pjaos/drive_mobility_scooter_battery_dock/schematic/drive_mobility_scooter_battery_dock.kicad_sch

## KiCad design schematic/drive_mobility_scooter_battery_dock.kicad_sch (2025-09-18, an earlier design)

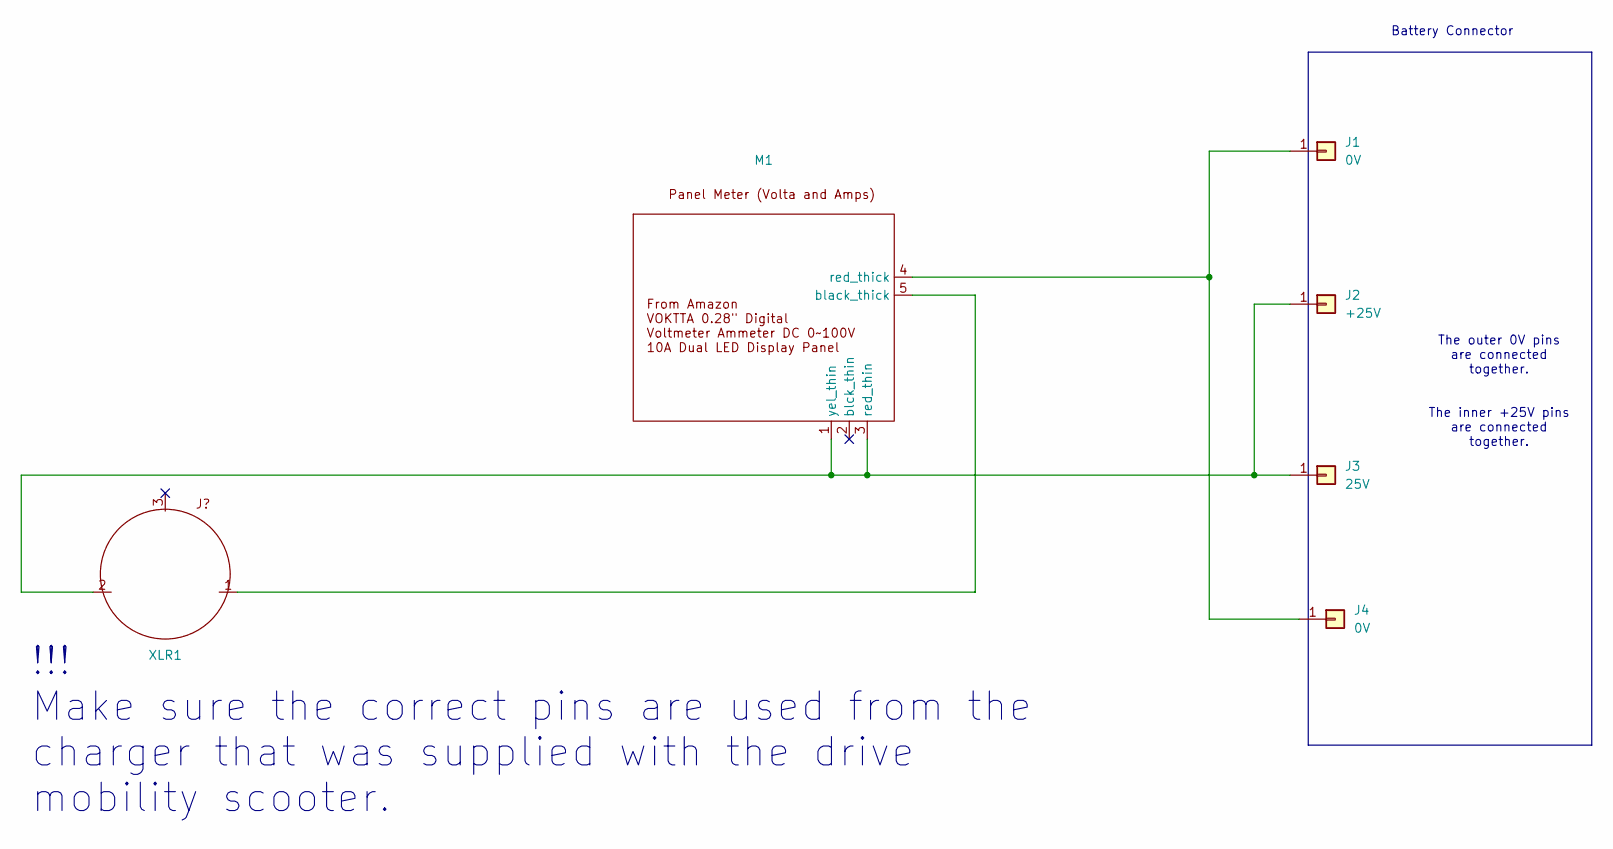
[picture p12: schematic drive_mobility_scooter_battery_dock.kicad_sch]

Parts:
J1, J4: 0V
J2: +25V
J3: 25V
M1: (no value)
XLR1: (no value)

Connections:
unnamed: J1.1, J4.1, M1.4 (red_thick)
unnamed: J2.1, J3.1, M1.1 (yel_thin), M1.3 (red_thin), XLR1.2
unnamed: M1.5 (black_thick), XLR1.1

Notes on the sheet:
Battery Connector
!!! Make sure the correct pins are used from the charger that was supplied with the drive mobility scooter.
The outer 0V pins are connected together. The inner +25V pins are connected together.
